BasicAirData/AirDataComputer/Hardware/3D support/MICRO SD ADAPTER/images/sd_adaptor_bottom.jpg

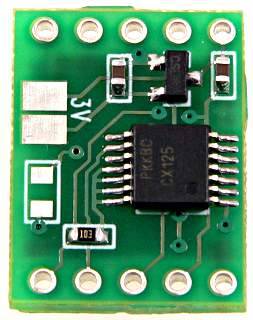
Hardware/3D support/MICRO SD ADAPTER/images/sd_adaptor_bottom.jpg
