BasicAirData/AirDataComputer/Hardware/3D support/MICRO SD ADAPTER/images/sd_adaptor_top.jpg

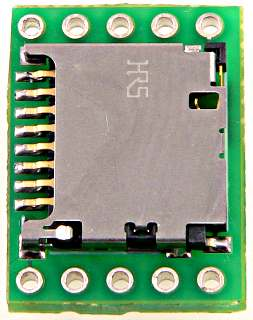
Hardware/3D support/MICRO SD ADAPTER/images/sd_adaptor_top.jpg
