BasicAirData/AirDataComputer/Hardware/kicad/Asgard/common COTS/Absolutepressure.png

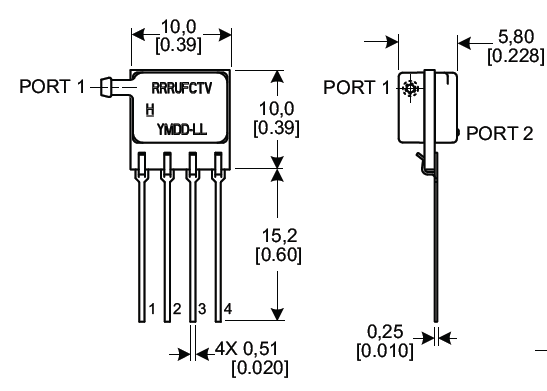
Hardware/kicad/Asgard/common COTS/Absolutepressure.png
