BasicAirData/AirDataComputer/Hardware/kicad/Asgard/common COTS/Bluesmirfbottom.jpg

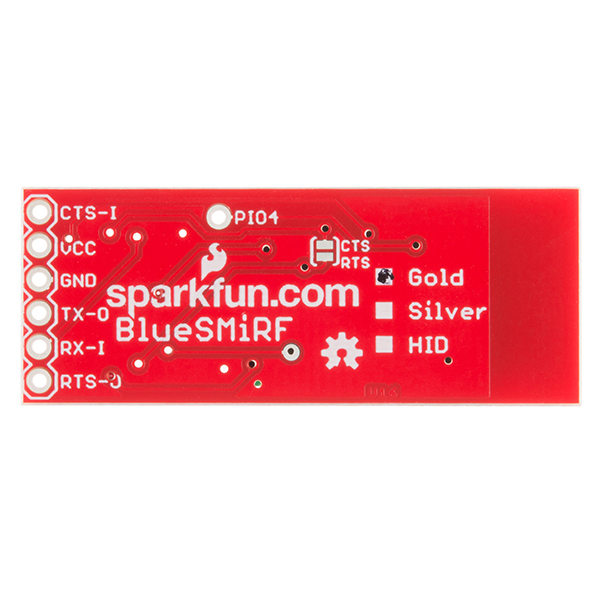
Hardware/kicad/Asgard/common COTS/Bluesmirfbottom.jpg
