BasicAirData/AirDataComputer/Hardware/kicad/Asgard/common COTS/Bluesmirfup12582-02.jpg

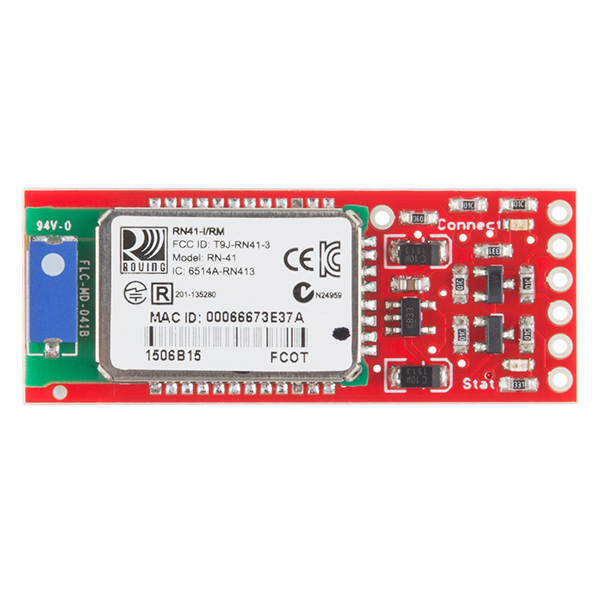
Hardware/kicad/Asgard/common COTS/Bluesmirfup12582-02.jpg
