BasicAirData/AirDataComputer/Hardware/kicad/Asgard/common COTS/differentialpressure.png

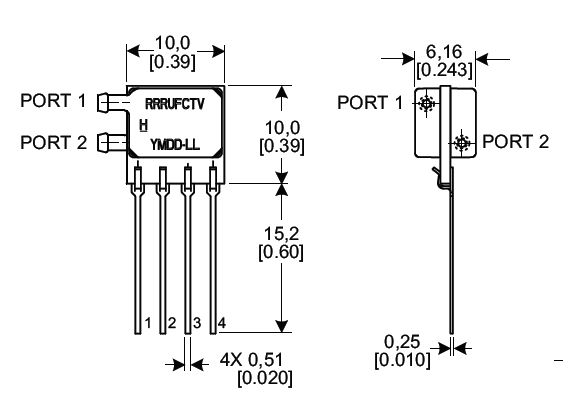
Hardware/kicad/Asgard/common COTS/differentialpressure.png
