BasicAirData/AirDataComputer/Hardware/kicad/Asgard/common COTS/HC-05 91D8m7vTveL._SL1500_.jpg

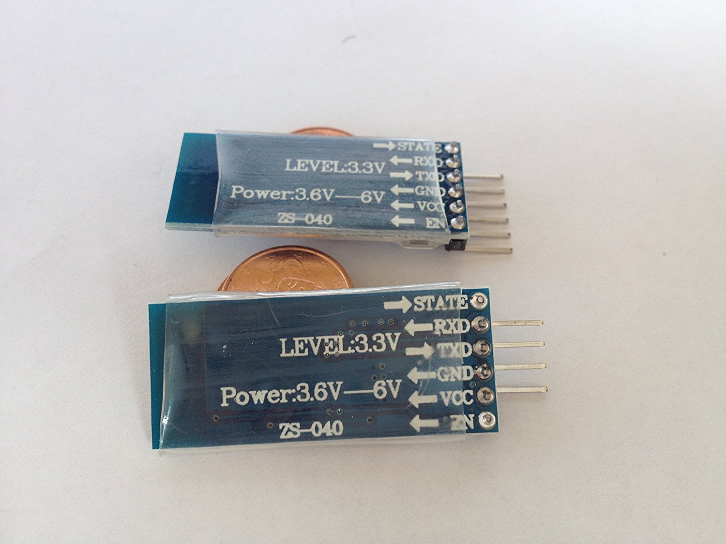
Hardware/kicad/Asgard/common COTS/HC-05 91D8m7vTveL._SL1500_.jpg
