BasicAirData/AirDataComputer/Hardware/kicad/Asgard/common COTS/TMP3536pinout.png

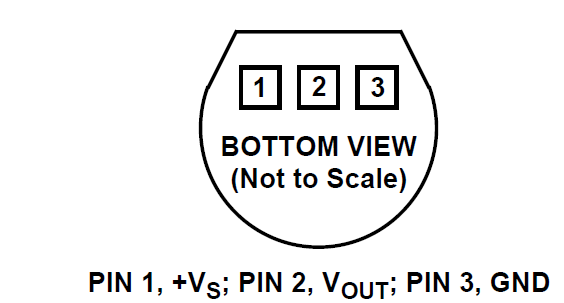
Hardware/kicad/Asgard/common COTS/TMP3536pinout.png
