BasicAirData/AirDataComputer/Software/Documentation/Firmware/Diagram/Acquire Sensors Data.jpg

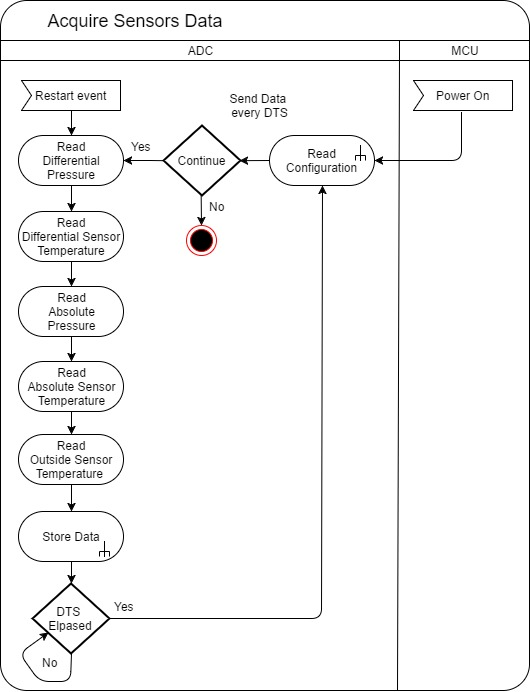
Software/Documentation/Firmware/Diagram/Acquire Sensors Data.jpg
