BasicAirData/AirDataComputer/Software/Documentation/Firmware/Diagram/Compute Air Data.jpg

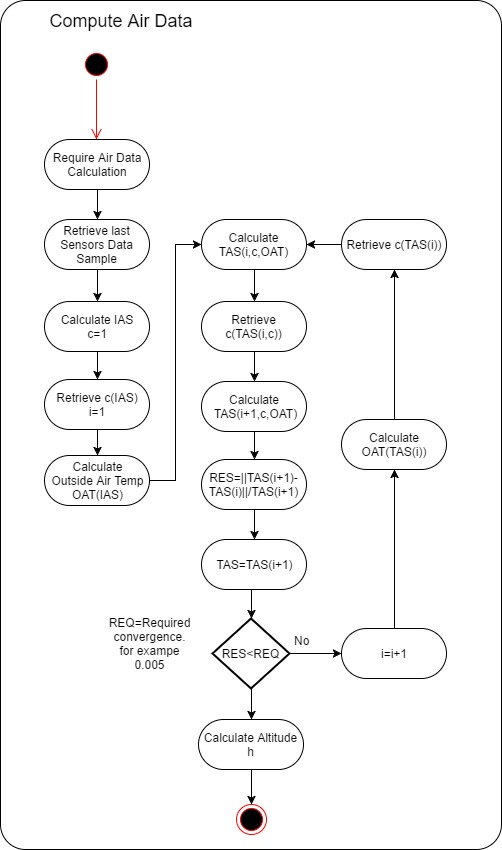
Software/Documentation/Firmware/Diagram/Compute Air Data.jpg
