BasicAirData/AirDataComputer/Software/Documentation/Firmware/Diagram/Configuration.jpg

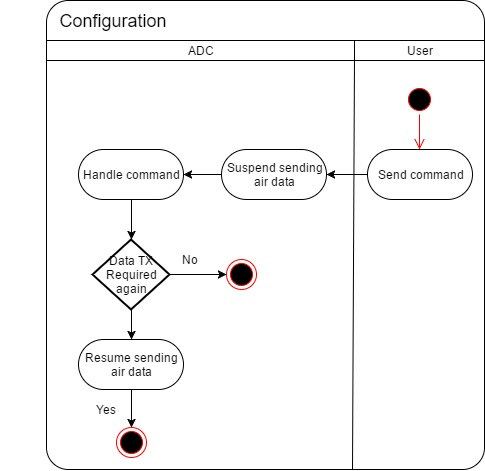
Software/Documentation/Firmware/Diagram/Configuration.jpg
