BasicAirData/AirDataComputer/Software/Documentation/Firmware/Diagram/Receive Data Periodically.jpg

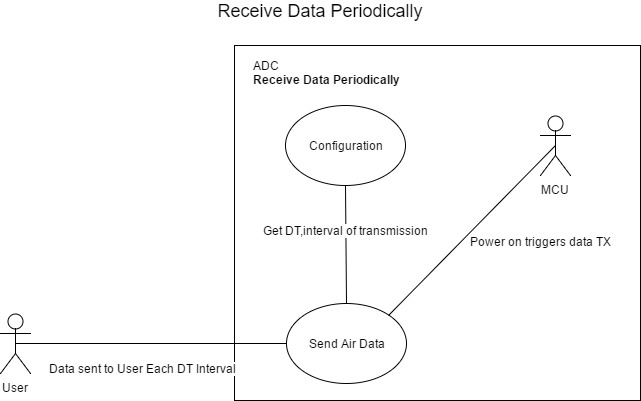
Software/Documentation/Firmware/Diagram/Receive Data Periodically.jpg
