BasicAirData/AirDataComputer/Software/Documentation/Firmware/Diagram/Send Air Data.jpg

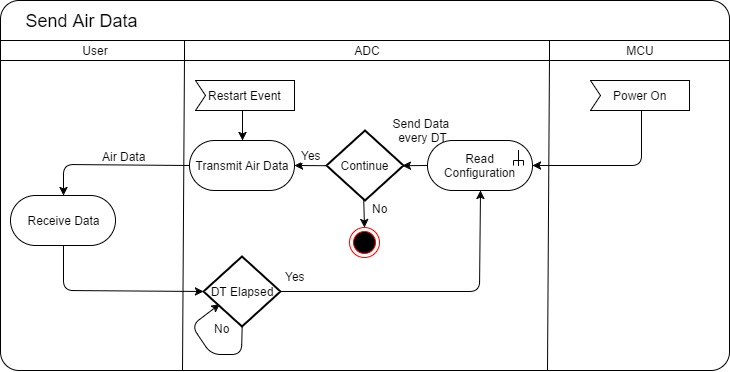
Software/Documentation/Firmware/Diagram/Send Air Data.jpg
