BasicAirData/AirDataComputer/Software/Documentation/Firmware/Diagram/Store Data.jpg

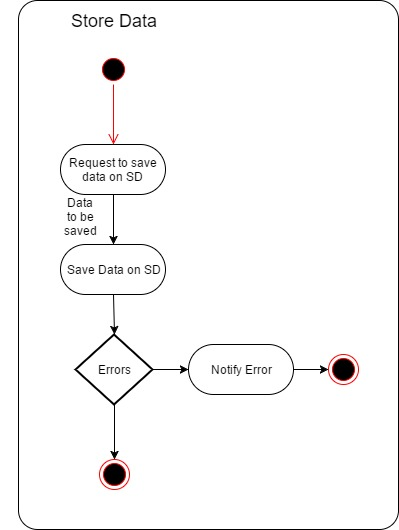
Software/Documentation/Firmware/Diagram/Store Data.jpg
