BasicAirData/AirDataComputer/Software/Documentation/Firmware/Diagram/Use Case Configuration.jpg

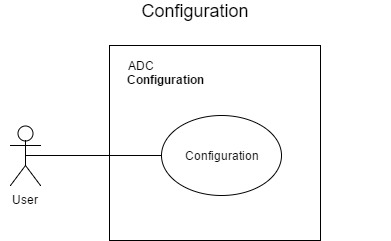
Software/Documentation/Firmware/Diagram/Use Case Configuration.jpg
