BasicAirData/AirDataComputer/Software/Documentation/Miscellaneous/curvec.png

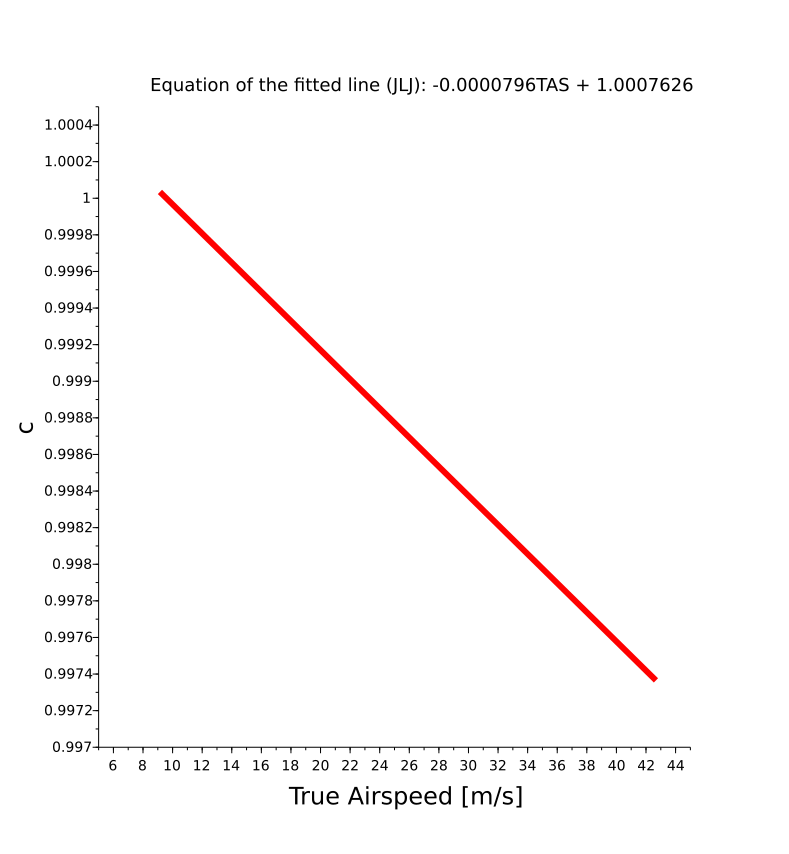
Software/Documentation/Miscellaneous/curvec.png
