BasicAirData/AirDataComputer/Software/Script/Scilab/ADCAsgard/Figures/GPS Speed vs Pitot Speed and Difference.png

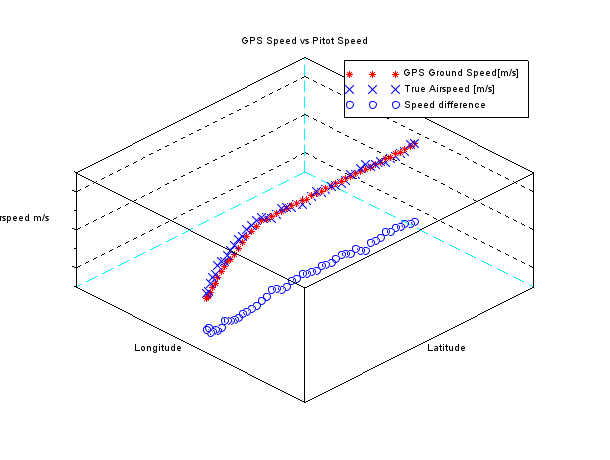
Software/Script/Scilab/ADCAsgard/Figures/GPS Speed vs Pitot Speed and Difference.png
