BasicAirData/AirDataComputer/Software/Script/Scilab/ADCAsgard/Figures/GPS Speed vs Pitot Speed.png

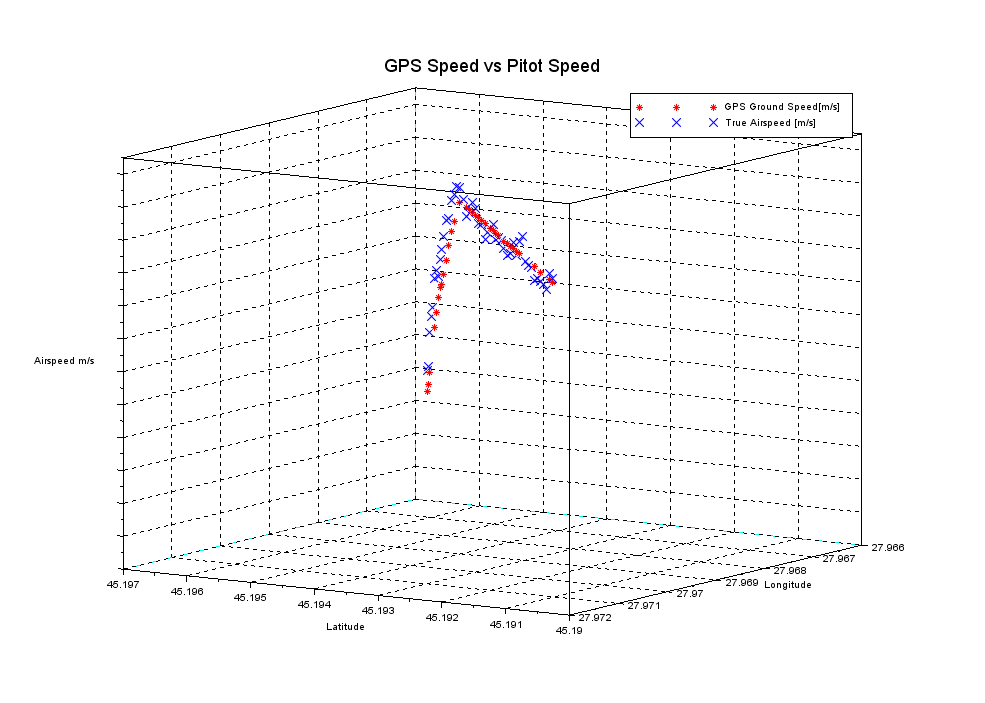
Software/Script/Scilab/ADCAsgard/Figures/GPS Speed vs Pitot Speed.png
