BasicAirData/AirDataComputer/Software/Script/Scilab/ADCAsgard/Figures/QGIS.png

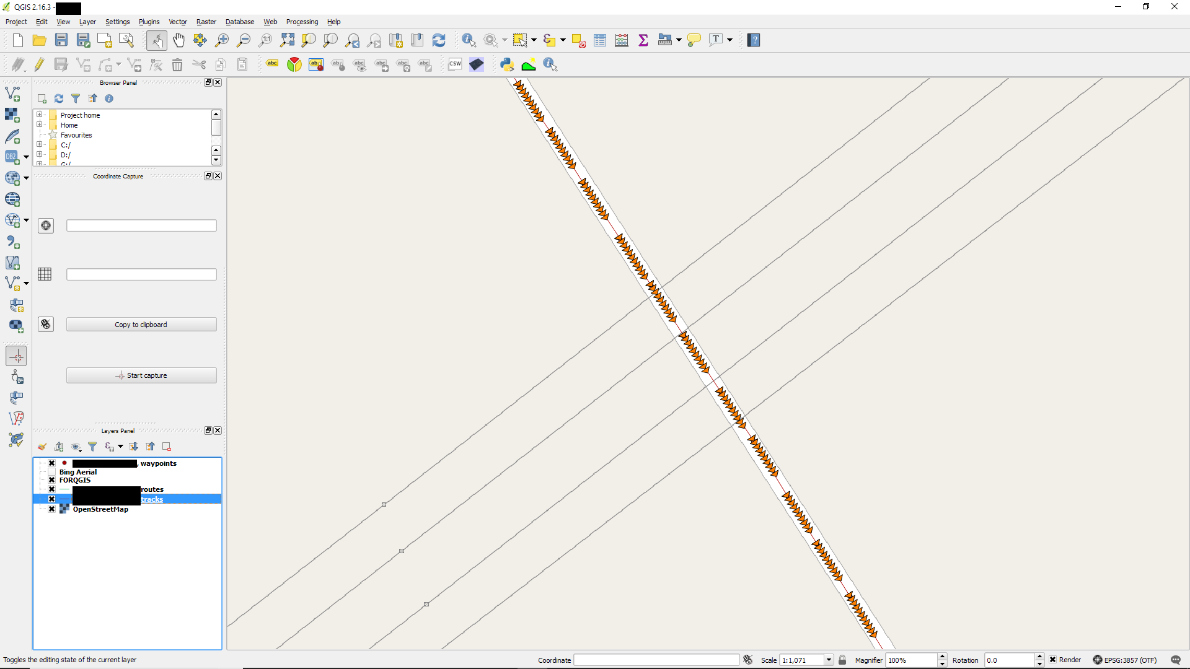
Software/Script/Scilab/ADCAsgard/Figures/QGIS.png
